codedstructureslab/Sensor-Sticker/Skin-Sensor/V1/fw/board_def/samd/variants/atsamd21e18a/variant.cpp

/*
  Copyright (c) 2014-2015 Arduino LLC.  All right reserved.

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
  You should have received a copy of the GNU Lesser General Public
  License along with this library; if not, write to the Free Software
  Foundation, Inc., 51 Franklin St, Fifth Floor, Boston, MA  02110-1301  USA
*/
/* NOTE: PA14/PA15 are used by external clock source.
 * PA15 may be pulled low to stay in SAM-BA bootloader mode (to upload another sketch via BOSSA utility)
 * PA30 (SWCLK)/PA31 (SWDIO) are reserved for SWD JTAG.
 * +------------+------------------+--------+-----------------+--------------------------------------------------------------------------------------------------------
 * + Pin number +  SAMD21E18A pin  |  PIN   | Label/Name      | Comments (* is for default peripheral in use)
 * +------------+------------------+--------+-----------------+--------------------------------------------------------------------------------------------------------
 * |            | Digital Low      |        |                 |
 * +------------+------------------+--------+-----------------+--------------------------------------------------------------------------------------------------------
 * | 0          | 0 -> RX          |  PA11  | RX              | EIC/EXTINT[11] ADC/AIN[19]           PTC/X[3] *SERCOM0/PAD[3]  SERCOM2/PAD[3]  TCC0/WO[3]  TCC1/WO[1]
 * | 1          | 1 <- TX          |  PA10  | TX              | EIC/EXTINT[10] ADC/AIN[18]           PTC/X[2] *SERCOM0/PAD[2]                  TCC0/WO[2]  TCC1/WO[0]
 * | 2          | 2                |  PA00  |                 | EIC/EXTINT[0]                                    SERCOM4/PAD[2]  TC3/WO[0]   TCC0/WO[4] (32KHz config was EIC/EXTINT[0] SERCOM1/PAD[0] TCC2/WO[0])
 * | 3          | ~3               |  PA09  | Green           | EIC/EXTINT[9]  ADC/AIN[17]           PTC/X[1]  SERCOM0/PAD[1]  SERCOM2/PAD[1] *TCC0/WO[1]  TCC1/WO[3]
 * | 4          | ~4               |  PA08  | Red             | EIC/NMI        ADC/AIN[16]           PTC/X[0]  SERCOM0/PAD[0]  SERCOM2/PAD[0] *TCC0/WO[0]  TCC1/WO[2]
 * | 5          | 5                |  PA27  |                 | EIC/EXTINT[15]
 * | 6          | 6                |  PA01  |                 | EIC/EXTINT[1]                                                  SERCOM1/PAD[1] (32KHz config was EIC/EXTINT[1] SERCOM1/PAD[1] TCC2/WO[1])
 * +------------+------------------+--------+-----------------+--------------------------------------------------------------------------------------------------------
 * |            | Digital High     |        |                 |
 * +------------+------------------+--------+-----------------+--------------------------------------------------------------------------------------------------------
 * | 7          | ~7               |  PA18  | SS              | EIC/EXTINT[2]                        PTC/X[6] +SERCOM1/PAD[2]  SERCOM3/PAD[2] *TC3/WO[0]    TCC0/WO[2]
 * | 8          | ~8               |  PA16  | MOSI            | EIC/EXTINT[0]                        PTC/X[4] +SERCOM1/PAD[0]  SERCOM3/PAD[0] *TCC2/WO[0]   TCC0/WO[6]
 * | 9          | ~9               |  PA19  | MISO            | EIC/EXTINT[3]                        PTC/X[7] +SERCOM1/PAD[3]  SERCOM3/PAD[3]  TC3/WO[1]   *TCC0/WO[3]
 * | 10         | ~10              |  PA17  | SCK/Blue        | EIC/EXTINT[1]                        PTC/X[5] +SERCOM1/PAD[1]  SERCOM3/PAD[1] *TCC2/WO[1]   TCC0/WO[7]
 * +------------+------------------+--------+-----------------+--------------------------------------------------------------------------------------------------------
 * |            | Analog Connector |        |                 |
 * +------------+------------------+--------+-----------------+--------------------------------------------------------------------------------------------------------
 * | 11         | A0/DAC           |  PA02  | A0              | EIC/EXTINT[2] *ADC/AIN[0]  DAC/VOUT  PTC/Y[0]
 * | 12         | A1               |  PA06  | A1              | EIC/EXTINT[6] *ADC/AIN[6]            PTC/Y[4]  SERCOM0/PAD[2]                  TC1/WO[0]
 * | 13         | A2               |  PA07  | A2              | EIC/EXTINT[9] *ADC/AIN[3]            PTC/Y[5]  SERCOM0/PAD[3]                  TC1/WO[1]
 * | 14         | A3               |  PA04  | A3              | EIC/EXTINT[4] *ADC/AIN[4]  AC/AIN[0] PTC/Y[2]  SERCOM0/PAD[0]                  TCC0/WO[0]
 * | 15         | A4               |  PA05  | A4              | EIC/EXTINT[5] *ADC/AIN[5]  AC/AIN[1] PTC/Y[3]  SERCOM0/PAD[1]                  TCC0/WO[1]
 * +------------+------------------+--------+-----------------+--------------------------------------------------------------------------------------------------------
 * |            | Wire             |        |                 |
 * +------------+------------------+--------+-----------------+--------------------------------------------------------------------------------------------------------
 * | 16         | SDA              |  PA22  | SDA             | EIC/EXTINT[6]                        PTC/X[10] *SERCOM3/PAD[0] SERCOM5/PAD[0] TC4/WO[0] TCC0/WO[4]
 * | 17         | SCL              |  PA23  | SCL             | EIC/EXTINT[7]                        PTC/X[11] *SERCOM3/PAD[1] SERCOM5/PAD[1] TC4/WO[1] TCC0/WO[5]
 * +------------+------------------+--------+-----------------+--------------------------------------------------------------------------------------------------------
 * |            |SPI (Legacy ICSP) |        |                 |
 * +------------+------------------+--------+-----------------+--------------------------------------------------------------------------------------------------------
 * | 18         | 1                |  PA19  | MISO            | EIC/EXTINT[3] *SERCOM1/PAD[3] SERCOM3/PAD[3] TC3/WO[1]  TCC0/WO[3]
 * |            | 2                |        | 3V0             |
 * | 19         | 4                |  PA16  | MOSI            | EIC/EXTINT[0] *SERCOM1/PAD[0] SERCOM3/PAD[0] TCC2/WO[0] TCC0/WO[6]
 * | 20         |                  |  PA18  | SS              | EIC/EXTINT[2] *SERCOM1/PAD[2] SERCOM3/PAD[2] TC3/WO[0]  TCC0/WO[2]
 * | 21         | 3                |  PA17  | SCK             | EIC/EXTINT[1] *SERCOM1/PAD[1] SERCOM3/PAD[1] TCC2/WO[1] TCC0/WO[7]
 * |            | 5                |        | RESET           |
 * |            | 6                |        | GND             |
 * +------------+------------------+--------+-----------------+--------------------------------------------------------------------------------------------------------
 * |            | USB              |        |                 |
 * +------------+------------------+--------+-----------------+--------------------------------------------------------------------------------------------------------
 * | 22         |                  |  PA28  | USB_HOST_ENABLE | EIC/EXTINT[8]
 * | 23         |                  |  PA24  | USB_NEGATIVE    | *USB/DM
 * | 24         |                  |  PA25  | USB_POSITIVE    | *USB/DP
 * +------------+------------------+--------+-----------------+--------------------------------------------------------------------------------------------------------
 * |            |                  |        |                 |
 * +------------+------------------+--------+-----------------+--------------------------------------------------------------------------------------------------------
 * |            | GND              |        |                 |
 * | 25         | AREF             |  PA03  | AREF            | EIC/EXTINT[3] *[ADC|DAC]/VREFA ADC/AIN[1] PTC/Y[1]
 * +------------+------------------+--------+-----------------+--------------------------------------------------------------------------------------------------------
 */

#include <Arduino.h>
#include "variant.h"
/*
 * Pins descriptions
 */
const PinDescription g_APinDescription[]=
{
/* APA PORT 0
 * +------------+------------------+--------+-----------------+--------------------------------------------------------------------------------------------------------
 * | Pin number | Serial           |  PIN   | Label/Name      | Comments (* is for default peripheral in use)
 * +------------+------------------+--------+-----------------+--------------------------------------------------------------------------------------------------------
 * | 0          |                  |  PA05  | RX              | EXTINT[1]      PTC/Y[3]                  SERCOM0_ALT[PAD1]  TCC0/WO[1]  *TCC0_ALT/WO[1] 
 * | 1          |                  |  PA04  | TX              |                PTC/Y[2]                  SERCOM0_ALT[PAD0]  TCC0/WO[0]  *TCC0_ALT/WO[0] 
 * +------------+------------------+--------+-----------------+--------------------------------------------------------------------------------------------------------
 */
  { PORTA,  5, PIO_SERCOM_ALT, (PIN_ATTR_DIGITAL), No_ADC_Channel, NOT_ON_PWM, NOT_ON_TIMER, EXTERNAL_INT_5 },
  { PORTA,  4, PIO_SERCOM_ALT, (PIN_ATTR_DIGITAL), No_ADC_Channel, NOT_ON_PWM, NOT_ON_TIMER, EXTERNAL_INT_4 },

/* APA PORT 1
 * +------------+------------------+--------+-----------------+--------------------------------------------------------------------------------------------------------
 * | Pin number | Serial           |  PIN   | Label/Name      | Comments (* is for default peripheral in use)
 * +------------+------------------+--------+-----------------+--------------------------------------------------------------------------------------------------------
 * | 2          |                  |  PA17  | RX              | EXTINT[1]      PTX/X[5]  SERCOM1/PAD[1]  SERCOM3_ALT[PAD1]  TCC2/WO[1]  *TCC0_ALT/WO[1] GCLK_IO[3]
 * | 3          |                  |  PA16  | TX              |                PTC/X[4]  SERCOM1/PAD[0]  SERCOM3_ALT[PAD0]  TCC2/WO[0]  *TCC0_ALT/WO[0] GCLK_IO[2]
 * +------------+------------------+--------+-----------------+--------------------------------------------------------------------------------------------------------
 */
  { PORTA, 17, PIO_SERCOM, (PIN_ATTR_DIGITAL), No_ADC_Channel, NOT_ON_PWM, NOT_ON_TIMER, EXTERNAL_INT_1 }, // RX: SERCOM1/PAD[1]
  { PORTA, 16, PIO_SERCOM, (PIN_ATTR_DIGITAL), No_ADC_Channel, NOT_ON_PWM, NOT_ON_TIMER, EXTERNAL_INT_0 }, // TX: SERCOM1/PAD[0]

/* APA PORT 2
 * +------------+------------------+--------+-----------------+--------------------------------------------------------------------------------------------------------
 * | Pin number | Serial           |  PIN   | Label/Name      | Comments (* is for default peripheral in use)
 * +------------+------------------+--------+-----------------+--------------------------------------------------------------------------------------------------------
 * | 4          |                  |  PA09  | RX              | EXTINT[1]      PTX/X[5]  SERCOM1/PAD[1]  SERCOM3_ALT[PAD1]  TCC2/WO[1]  *TCC0_ALT/WO[1] GCLK_IO[3]
 * | 5          |                  |  PA08  | TX              |                PTC/X[4]  SERCOM1/PAD[0]  SERCOM3_ALT[PAD0]  TCC2/WO[0]  *TCC0_ALT/WO[0] GCLK_IO[2]
 * +------------+------------------+--------+-----------------+--------------------------------------------------------------------------------------------------------
 */
  { PORTA,  9, PIO_SERCOM_ALT, (PIN_ATTR_DIGITAL), No_ADC_Channel, PWM0_CH1, TCC0_CH1, EXTERNAL_INT_9 }, // TCC0/WO[1]
  { PORTA,  8, PIO_SERCOM_ALT, (PIN_ATTR_DIGITAL), No_ADC_Channel, PWM0_CH0, TCC0_CH0, EXTERNAL_INT_NMI },  // TCC0/WO[0]

/*
 * +------------+------------------+--------+-----------------+--------------------------------------------------------------------------------------------------------
 * | Pin number | Wire             |  PIN   | Label/Name      | Comments (* is for default peripheral in use)
 * +------------+------------------+--------+-----------------+--------------------------------------------------------------------------------------------------------
 * | 6          | SCL              |  PA23  |                 | EIC/EXTINT[9] *ADC/AIN[17]  PTC/X[1]  SERCOM0/PAD[1] SERCOM2_ALT/PAD[1] TCC0/WO/[1]  FECTRL[1]
 * | 7          | SDA              |  PA22  | EXT3_10         | EIC/NMI  ADC/AIN[16]  PTC/X[0]  SERCOM0/PAD[0]  SERCOM2_ALT/PAD[0]  TCC0/WO[0]  FECTRL[0]
 * +------------+------------------+--------+-----------------+--------------------------------------------------------------------------------------------------------
 */
  { PORTA, 23, PIO_SERCOM, PIN_ATTR_DIGITAL, No_ADC_Channel, NOT_ON_PWM, NOT_ON_TIMER, EXTERNAL_INT_NONE }, //SCL
  { PORTA, 22, PIO_SERCOM, PIN_ATTR_DIGITAL, No_ADC_Channel, NOT_ON_PWM, NOT_ON_TIMER, EXTERNAL_INT_NONE }, //SDA
/* +------------+------------------+--------+-----------------+--------------------------------------------------------------------------------------------------------
 * | Pin number | USB              |  PIN   | Label/Name      | Comments (* is for default peripheral in use)
 * +------------+------------------+--------+-----------------+--------------------------------------------------------------------------------------------------------
 * |  8         |                  |  PA25  | USB_POSITIVE    | *USB/DP
 * |  9         |                  |  PA24  | USB_NEGATIVE    | *USB/DM
 * | 10         |                  |  PA28  | USB_HOST_ENABLE | USB/VBUS | EXT1_6          | EIC/EXTINT[8]  GCLK_IO[0]
 * +------------+------------------+--------+-----------------+--------------------------------------------------------------------------------------------------------
 */
  { PORTA, 25, PIO_COM, PIN_ATTR_NONE, No_ADC_Channel, NOT_ON_PWM, NOT_ON_TIMER, EXTERNAL_INT_NONE }, // USB/DP
  { PORTA, 24, PIO_COM, PIN_ATTR_NONE, No_ADC_Channel, NOT_ON_PWM, NOT_ON_TIMER, EXTERNAL_INT_NONE }, // USB/DM
  { PORTA, 28, PIO_COM, PIN_ATTR_NONE, No_ADC_Channel, NOT_ON_PWM, NOT_ON_TIMER, EXTERNAL_INT_NONE }, // USB Host enable

/*
 * +------------+------------------+--------+-----------------+--------------------------------------------------------------------------------------------------------
 * | Pin number | Analog pins      |  PIN   | Label/Name      | Comments (* is for default peripheral in use)
 * +------------+------------------+--------+-----------------+--------------------------------------------------------------------------------------------------------
 * | 11         |                  |  PA02  | A0              | EIC/EXTINT[6] *ADC/AIN[6]  AC/AIN[2]  PTC/Y[4]  SERCOM0_ALT/PAD[2]  TCC1/WO[0]
 * | 12         |                  |  PA03  | A1              | EIC/EXTINT[6] *ADC/AIN[6]  AC/AIN[2]  PTC/Y[4]  SERCOM0_ALT/PAD[2]  TCC1/WO[0]
 * | 13         |                  |  PA06  | A2              | EIC/EXTINT[6] *ADC/AIN[6]  AC/AIN[2]  PTC/Y[4]  SERCOM0_ALT/PAD[2]  TCC1/WO[0]
 * | 14         |                  |  PA07  | A3              | EIC/EXTINT[6] *ADC/AIN[6]  AC/AIN[2]  PTC/Y[4]  SERCOM0_ALT/PAD[2]  TCC1/WO[0]
 * +------------+------------------+--------+-----------------+--------------------------------------------------------------------------------------------------------
 */
  { PORTA,  2, PIO_ANALOG, PIN_ATTR_ANALOG, ADC_Channel0, NOT_ON_PWM, NOT_ON_TIMER, EXTERNAL_INT_2 }, // ADC/AIN[0] 
  { PORTA,  3, PIO_ANALOG, PIN_ATTR_ANALOG, ADC_Channel1, NOT_ON_PWM, NOT_ON_TIMER, EXTERNAL_INT_3 }, // ADC/AIN[0] 
  { PORTA,  6, PIO_ANALOG, PIN_ATTR_ANALOG, ADC_Channel6, PWM1_CH0, TCC1_CH0, EXTERNAL_INT_6 }, // TCC1/WO[0]
  { PORTA,  7, PIO_ANALOG, PIN_ATTR_ANALOG, ADC_Channel7, PWM1_CH1, TCC1_CH1, EXTERNAL_INT_7 }, // TCC1/WO[1]
  
//DIGITAL PINS 
// 15 THRU 22
  { PORTA, 10, PIO_SERCOM, (PIN_ATTR_DIGITAL), No_ADC_Channel, NOT_ON_PWM, NOT_ON_TIMER, EXTERNAL_INT_10 },
  { PORTA, 11, PIO_SERCOM, (PIN_ATTR_DIGITAL), No_ADC_Channel, NOT_ON_PWM, NOT_ON_TIMER, EXTERNAL_INT_11 },
  { PORTA, 14, PIO_DIGITAL, (PIN_ATTR_DIGITAL), No_ADC_Channel, NOT_ON_PWM, NOT_ON_TIMER, EXTERNAL_INT_14 },
  { PORTA, 15, PIO_TIMER, (PIN_ATTR_DIGITAL|PIN_ATTR_PWM|PIN_ATTR_TIMER), No_ADC_Channel, PWM3_CH1, TC3_CH1, EXTERNAL_INT_15 }, // TC3/WO[1]
  { PORTA, 20, PIO_TIMER_ALT, (PIN_ATTR_DIGITAL|PIN_ATTR_PWM|PIN_ATTR_TIMER_ALT), No_ADC_Channel, PWM0_CH6, TCC0_CH6, EXTERNAL_INT_4 }, // TCC0/WO[6]
  { PORTA, 21, PIO_DIGITAL, (PIN_ATTR_DIGITAL), No_ADC_Channel, NOT_ON_PWM, NOT_ON_TIMER, EXTERNAL_INT_5 },

  // Digital High
  { PORTA, 18, PIO_TIMER,     (PIN_ATTR_DIGITAL|PIN_ATTR_PWM|PIN_ATTR_TIMER), No_ADC_Channel, PWM3_CH0, TC3_CH0, EXTERNAL_INT_2 }, // TC3/WO[0]
  { PORTA, 19, PIO_TIMER_ALT, (PIN_ATTR_DIGITAL|PIN_ATTR_PWM|PIN_ATTR_TIMER_ALT), No_ADC_Channel, PWM0_CH3, TCC0_CH3, EXTERNAL_INT_3 }, // TCC0/WO[3]

  // 23 (AREF)
  { PORTA, 3, PIO_ANALOG, PIN_ATTR_ANALOG, No_ADC_Channel, NOT_ON_PWM, NOT_ON_TIMER, EXTERNAL_INT_NONE }, // DAC/VREFP

  // ----------------------
  // 24 - Alternate use of A0 (DAC output)
  { PORTA,  2, PIO_ANALOG, PIN_ATTR_ANALOG, DAC_Channel0, NOT_ON_PWM, NOT_ON_TIMER, EXTERNAL_INT_2 } // DAC/VOUT
} ;


const void* g_apTCInstances[TCC_INST_NUM+TC_INST_NUM]={ TCC0, TCC1, TCC2, TC3, TC4, TC5 } ;

// Multi-serial objects instantiation
SERCOM sercom0( SERCOM0 ) ;
SERCOM sercom1( SERCOM1 ) ;
SERCOM sercom2( SERCOM2 ) ;
SERCOM sercom3( SERCOM3 ) ;
// Uart Serial1( &sercom0, PIN_SERIAL1_RX, PIN_SERIAL1_TX, PAD_SERIAL1_RX, PAD_SERIAL1_TX ) ;
// Uart Serial( &sercom5, PIN_SERIAL_RX, PIN_SERIAL_TX, PAD_SERIAL_RX, PAD_SERIAL_TX ) ;

Uart APA0( &sercom0, PIN_APA0_RX, PIN_APA0_TX, PAD_APA0_RX, PAD_APA0_TX ) ;
Uart APA1( &sercom1, PIN_APA1_RX, PIN_APA1_TX, PAD_APA1_RX, PAD_APA1_TX ) ;
Uart APA2( &sercom2, PIN_APA2_RX, PIN_APA2_TX, PAD_APA2_RX, PAD_APA2_TX ) ;

// void SERCOM0_Handler()
// {
//   Serial1.IrqHandler();
// }

// void SERCOM5_Handler()
// {
//   Serial.IrqHandler();
// }
void SERCOM0_Handler()
{
  APA0.IrqHandler();
}

void SERCOM1_Handler()
{
  APA1.IrqHandler();
}

void SERCOM2_Handler()
{
  APA2.IrqHandler();
}
