codedstructureslab/Sensor-Sticker/Skin-Sensor/V1/fw/board_def/samd/variants/atsamd21e18a/variant.h

/*
  Copyright (c) 2014-2015 Arduino LLC.  All right reserved.

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
  You should have received a copy of the GNU Lesser General Public
  License along with this library; if not, write to the Free Software
  Foundation, Inc., 51 Franklin St, Fifth Floor, Boston, MA  02110-1301  USA
*/
 
#ifndef _VARIANT_ATSAMD21E18A_
#define _VARIANT_ATSAMD21E18A_

// The definitions here needs a SAMD core >=1.6.3
#define ARDUINO_SAMD_VARIANT_COMPLIANCE 10603

/*----------------------------------------------------------------------------
 *        Definitions
 *----------------------------------------------------------------------------*/

/** Frequency of the board main oscillator */
#define VARIANT_MAINOSC     (32768ul)

/** Master clock frequency */
#define VARIANT_MCK           (48000000ul)

/*----------------------------------------------------------------------------
 *        Headers
 *----------------------------------------------------------------------------*/

#include "WVariant.h"

#ifdef __cplusplus
#include "SERCOM.h"
#include "Uart.h"
#endif // __cplusplus

#ifdef __cplusplus
extern "C"
{
#endif // __cplusplus

/*----------------------------------------------------------------------------
 *        Pins
 *----------------------------------------------------------------------------*/

// Number of pins defined in PinDescription array
#define PINS_COUNT           (17u)
#define NUM_DIGITAL_PINS     (8u)
#define NUM_ANALOG_INPUTS    (4u)
#define NUM_ANALOG_OUTPUTS   (1u)
#define analogInputToDigitalPin(p)  ((p < 4u) ? (p) + 11u : -1)

#define digitalPinToPort(P)        ( &(PORT->Group[g_APinDescription[P].ulPort]) )
#define digitalPinToBitMask(P)     ( 1 << g_APinDescription[P].ulPin )
//#define analogInPinToBit(P)        ( )
#define portOutputRegister(port)   ( &(port->OUT.reg) )
#define portInputRegister(port)    ( &(port->IN.reg) )
#define portModeRegister(port)     ( &(port->DIR.reg) )
#define digitalPinHasPWM(P)        ( g_APinDescription[P].ulPWMChannel != NOT_ON_PWM || g_APinDescription[P].ulTCChannel != NOT_ON_TIMER )

/*
 * digitalPinToTimer(..) is AVR-specific and is not defined for SAMD
 * architecture. If you need to check if a pin supports PWM you must
 * use digitalPinHasPWM(..).
 *
 * https://github.com/arduino/Arduino/issues/1833
 */
// #define digitalPinToTimer(P)

// Interrupts
#define digitalPinToInterrupt(P)   ( g_APinDescription[P].ulExtInt )

// LEDs
// #define PIN_LED_10           (10u)
// #define PIN_LED_RXL          (25u)
// #define PIN_LED_TXL          (26u)
#define PIN_LED              (12u)
// #define PIN_LED2             PIN_LED_RXL
// #define PIN_LED3             PIN_LED_TXL
// #define LED_BUILTIN          PIN_LED_10

/*
 * Analog pins
 */
#define PIN_A0               (11ul)
#define PIN_A1               (12ul)
#define PIN_A2               (13ul)
#define PIN_A3               (14ul)
#define PIN_DAC0             (11ul)

static const uint8_t A0  = PIN_A0;
static const uint8_t A1  = PIN_A1;
static const uint8_t A2  = PIN_A2;
static const uint8_t A3  = PIN_A3;
static const uint8_t DAC0 = PIN_DAC0;

#define ADC_RESOLUTION		12

// Other pins
//#define PIN_ATN              (38ul)
//static const uint8_t ATN = PIN_ATN;

/*
 * Serial interfaces
 */

// APA0
#define PIN_APA0_RX       (0ul)
#define PIN_APA0_TX       (1ul)
#define PAD_APA0_TX       (UART_TX_PAD_0)
#define PAD_APA0_RX       (SERCOM_RX_PAD_1)

// APA1
#define PIN_APA1_RX       (2ul)
#define PIN_APA1_TX       (3ul)
#define PAD_APA1_TX       (UART_TX_PAD_0)
#define PAD_APA1_RX       (SERCOM_RX_PAD_1)

// APA2
#define PIN_APA2_RX       (4ul)
#define PIN_APA2_TX       (5ul)
#define PAD_APA2_TX       (UART_TX_PAD_0)
#define PAD_APA2_RX       (SERCOM_RX_PAD_1)

/*
 * SPI Interfaces
 */
#define SPI_INTERFACES_COUNT 0

#define PIN_SPI_MISO         (18u)
#define PIN_SPI_MOSI         (19u)
#define PIN_SPI_SCK          (21u)
#define PIN_SPI_SS           (20u)
#define PERIPH_SPI           sercom4
#define PAD_SPI_TX           SPI_PAD_2_SCK_3
#define PAD_SPI_RX           SERCOM_RX_PAD_0

static const uint8_t SS   = PIN_SPI_SS  ;
static const uint8_t MOSI = PIN_SPI_MOSI ;
static const uint8_t MISO = PIN_SPI_MISO ;
static const uint8_t SCK  = PIN_SPI_SCK ;

/*
 * Wire Interfaces
 */
#define WIRE_INTERFACES_COUNT 1

#define PIN_WIRE_SDA         (7u)
#define PIN_WIRE_SCL         (6u)
#define PERIPH_WIRE          sercom3
#define WIRE_IT_HANDLER      SERCOM3_Handler

/*
 * USB
 */
#define PIN_USB_HOST_ENABLE (10ul)
#define PIN_USB_DM           (9ul)
#define PIN_USB_DP           (8ul)

#ifdef __cplusplus
}
#endif

/*----------------------------------------------------------------------------
 *        Arduino objects - C++ only
 *----------------------------------------------------------------------------*/

#ifdef __cplusplus

/*  =========================
 *  ===== SERCOM DEFINITION
 *  =========================
*/
extern SERCOM sercom0;
extern SERCOM sercom1;
extern SERCOM sercom2;
extern SERCOM sercom3;

extern Uart APA0;
extern Uart APA1;
extern Uart APA2;
extern Uart Serial;
// extern Uart Serial1;

#endif

// These serial port names are intended to allow libraries and architecture-neutral
// sketches to automatically default to the correct port name for a particular type
// of use.  For example, a GPS module would normally connect to SERIAL_PORT_HARDWARE_OPEN,
// the first hardware serial port whose RX/TX pins are not dedicated to another use.
//
// SERIAL_PORT_MONITOR        Port which normally prints to the Arduino Serial Monitor
//
// SERIAL_PORT_USBVIRTUAL     Port which is USB virtual serial
//
// SERIAL_PORT_LINUXBRIDGE    Port which connects to a Linux system via Bridge library
//
// SERIAL_PORT_HARDWARE       Hardware serial port, physical RX & TX pins.
//
// SERIAL_PORT_HARDWARE_OPEN  Hardware serial ports which are open for use.  Their RX & TX
//                            pins are NOT connected to anything by default.
#define SERIAL_PORT_USBVIRTUAL      SerialUSB
#define Serial SerialUSB
// #define SERIAL_PORT_MONITOR         Serial
// // Serial has no physical pins broken out, so it's not listed as HARDWARE port
// #define SERIAL_PORT_HARDWARE        Serial1
// #define SERIAL_PORT_HARDWARE_OPEN   Serial1

#define SERIAL_PORT_MONITOR        Serial
// #define SERIAL_PORT_HARDWARE        Serial1
// #define SERIAL_PORT_HARDWARE_OPEN   Serial1

#endif /* _VARIANT_ATSAMD21E18A_ */
